0x544D/EthernetLEDCube/PCB/schaltplan.pdf

# Vorwiderstände: Rot: 129 Ohm -> 20 mA

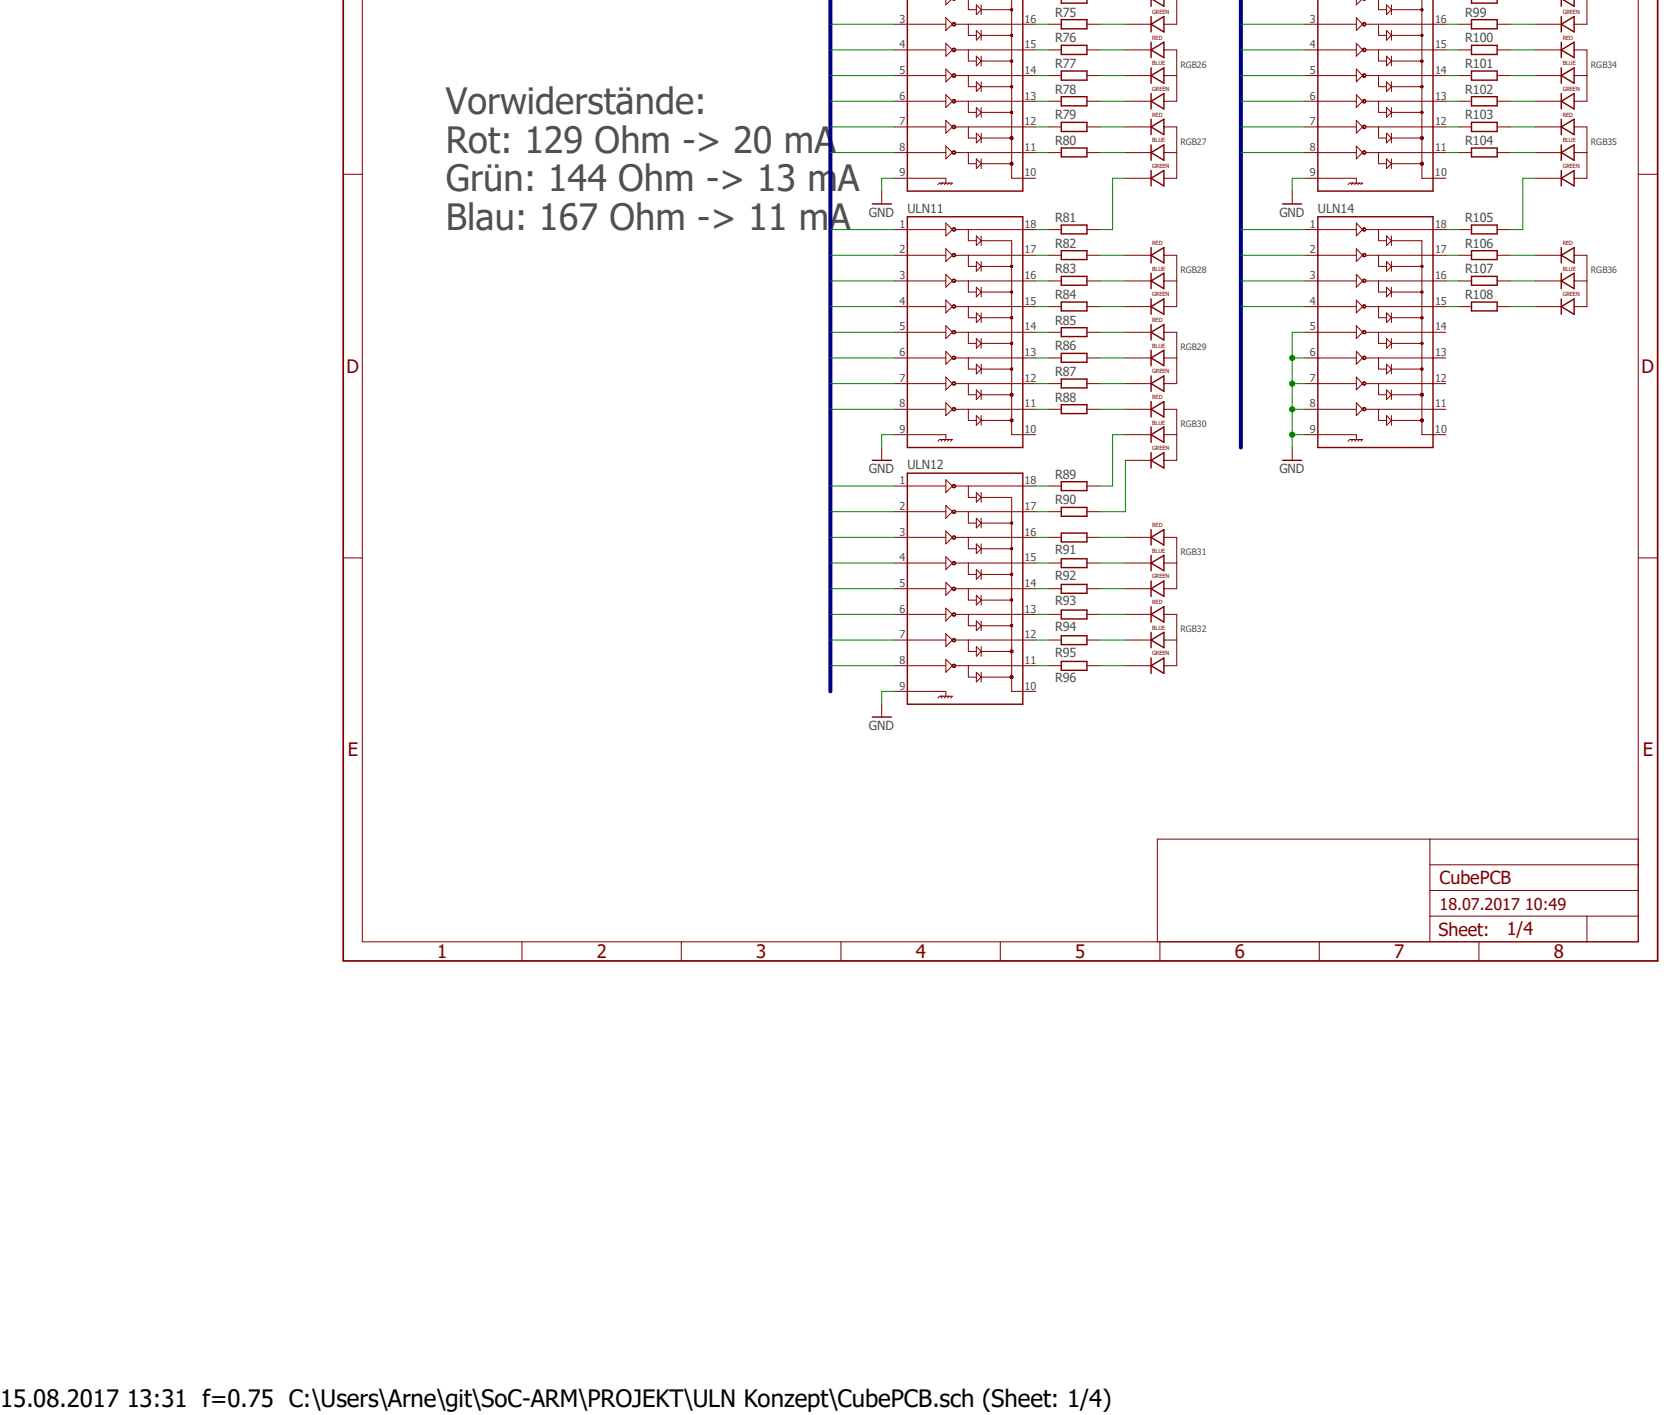
[picture p20: page 1]

Grün: 144 Ohm -> 13 mA
Blau: 167 Ohm -> 11 mA GND

15.08.2017 13:31 f=0.75 C:\Users\Arne\git\SoC-ARM\PROJEKT\ULN Konzept\CubePCB.sch (Sheet: 1/4)

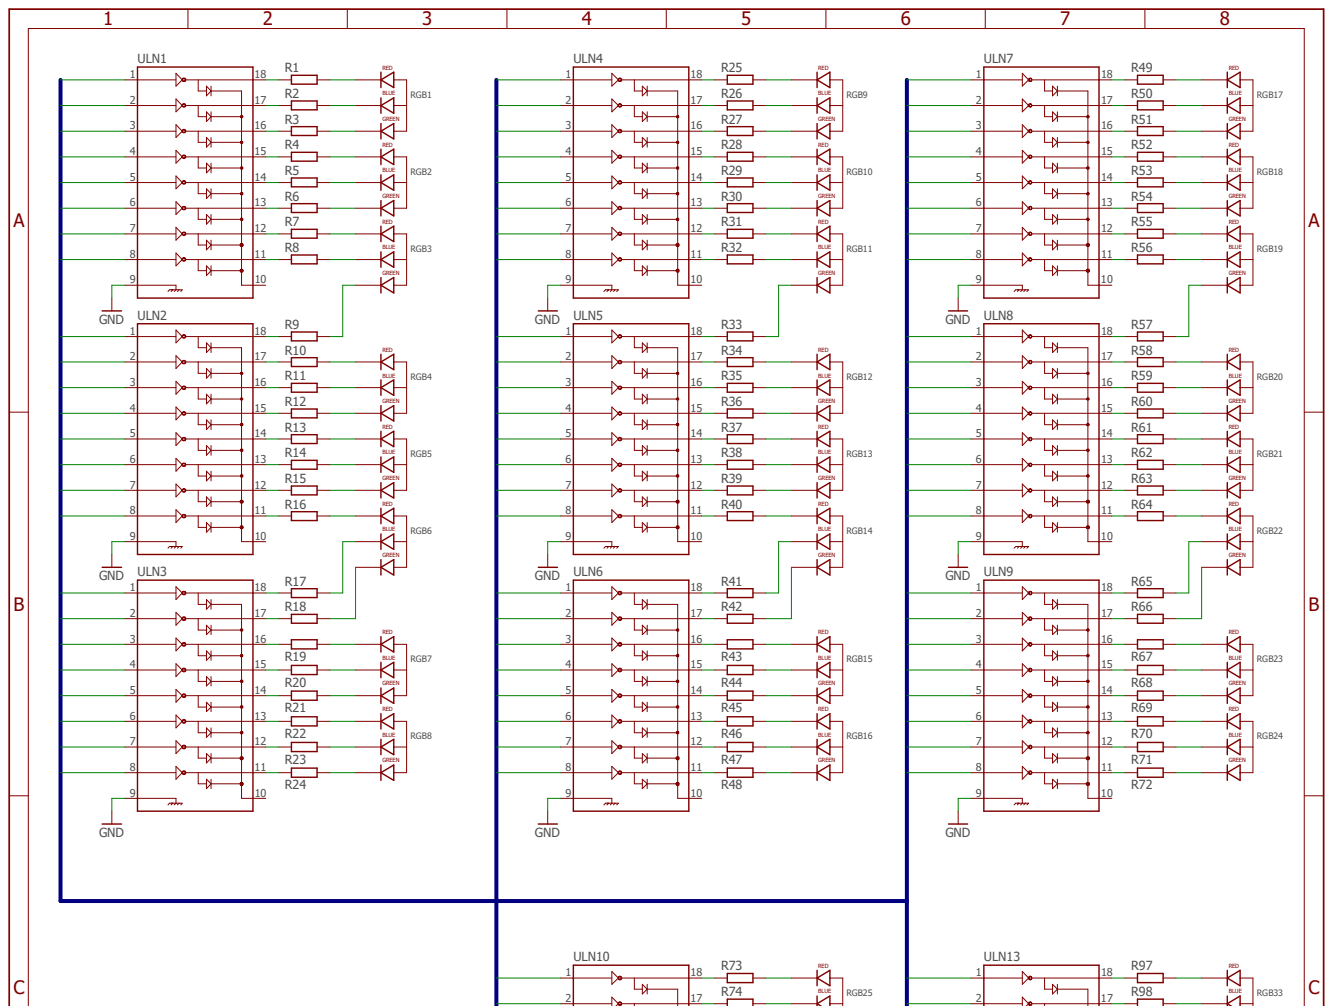
[picture p21: page 2]

# Q11 2 IC1A

A

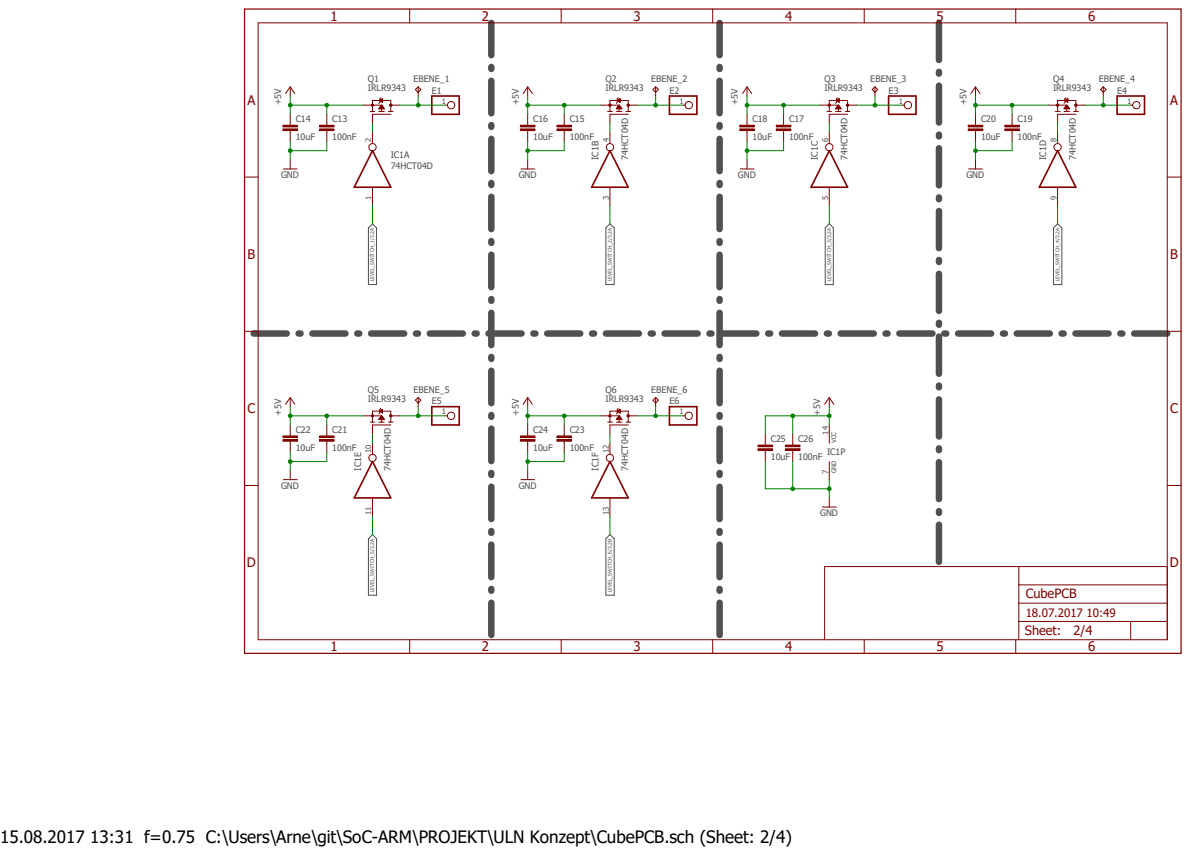
[picture p22: page 3]

EBENE_1 Q2 EBENE_2 Q3 EBENE_3 | Q4 EBENE_4

15.08.2017 13:31 f=0.75 C:\Users\Arne\git\SoC-ARM\PROJEKT\ULN Konzept\CubePCB.sch (Sheet: 2/4)

B36 ⁵V_FPGA_P2 | 3V3_FPGA_P2
B19 ⁵V_FPGA_P1 | 3V3_FPGA_P1 1

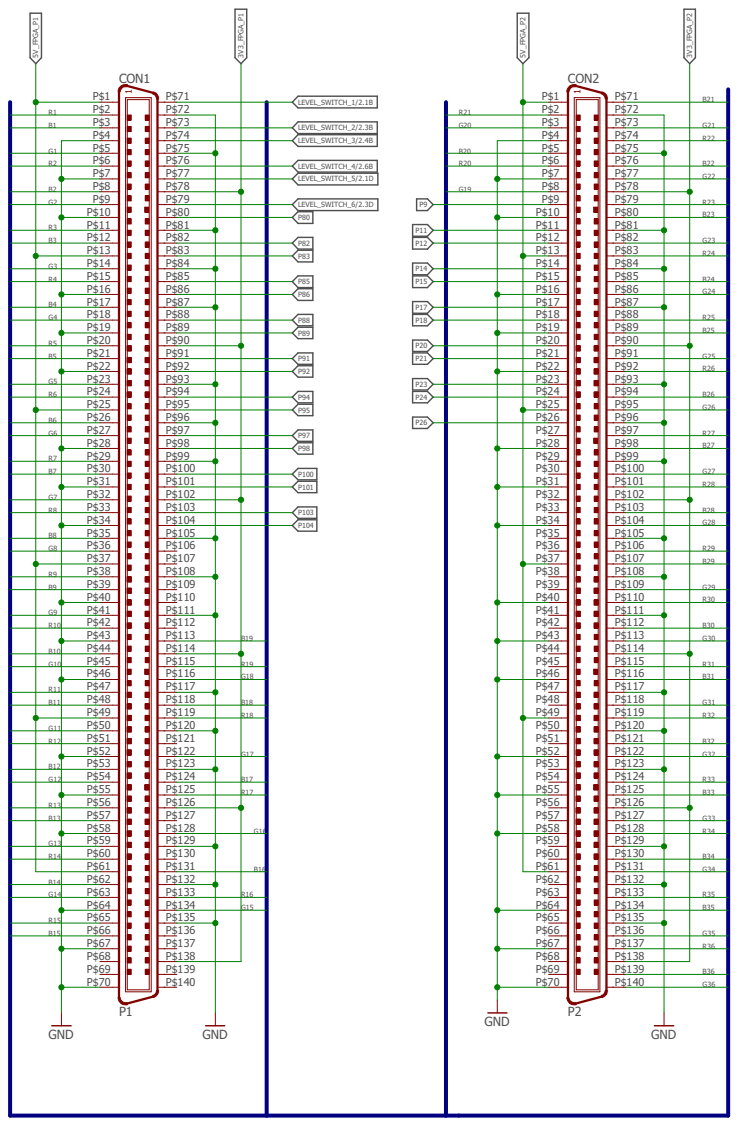
[picture p23: page 4]

15.08.2017 13:31 f=0.75 C:\Users\Arne\git\SoC-ARM\PROJEKT\ULN Konzept\CubePCB.sch (Sheet: 3/4)

A

A

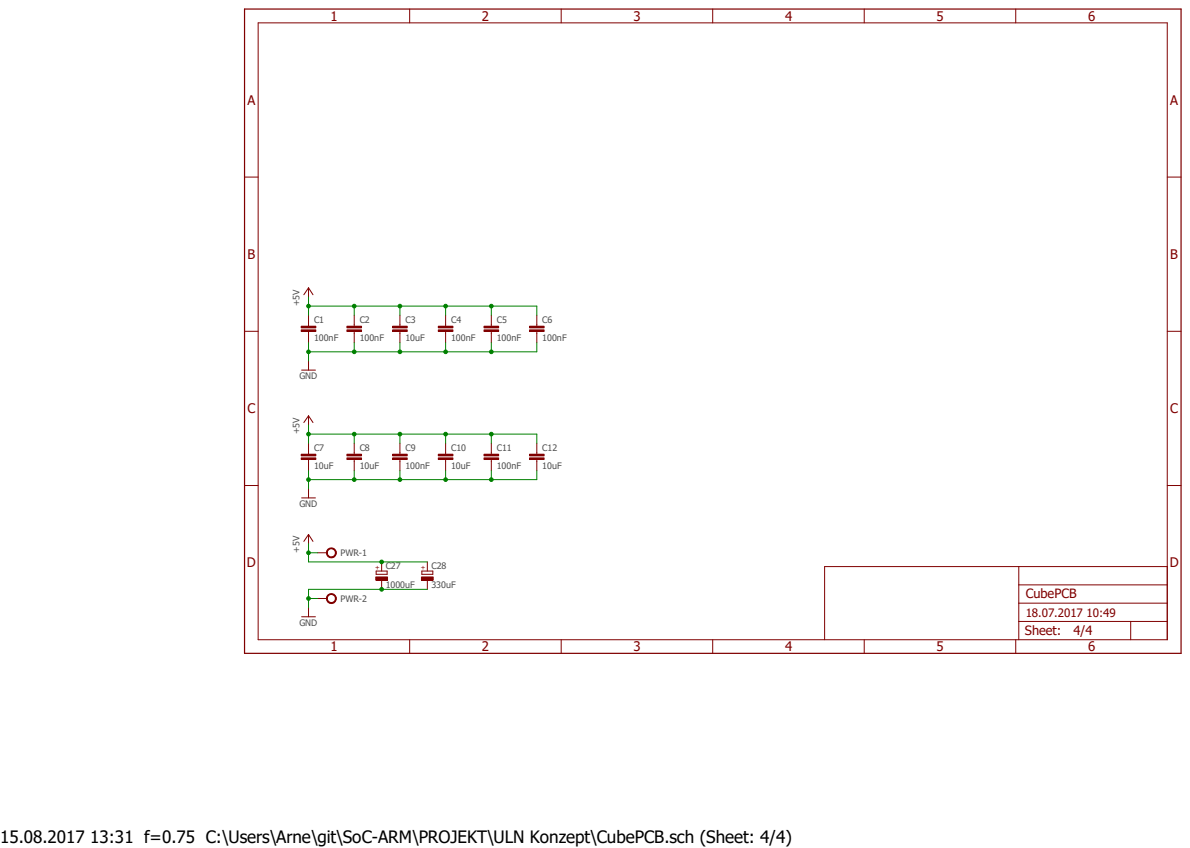
[picture p24: page 5]

15.08.2017 13:31 f=0.75 C:\Users\Arne\git\SoC-ARM\PROJEKT\ULN Konzept\CubePCB.sch (Sheet: 4/4) ⁺⁵V GND
