0x544D/EthernetLEDCube/software/v2/cube.h

#ifndef _CUBE_H
#define _CUBE_H

#include <arpa/inet.h>
#include <linux/if_packet.h>
#include <sys/ioctl.h>
#include <sys/socket.h>
#include <net/if.h>
#include <netinet/ether.h>

#define FPGA_MAC_ADDR0	0xaa
#define FPGA_MAC_ADDR1	0xaa
#define FPGA_MAC_ADDR2	0xaa
#define FPGA_MAC_ADDR3	0xaa
#define FPGA_MAC_ADDR4	0xaa
#define FPGA_MAC_ADDR5	0xaa

#define INTERFACE	"enp0s3"
#define BUF_SIZ		122

#define BUF_PAYLOAD_BEGIN	14
#define CUBE_DIM	6
#define PWM_STEPS	256

typedef struct {
	uint8_t r;
	uint8_t g;
	uint8_t b;
} led;

typedef struct {
	uint16_t h;
	float s;
	float v;
} hsvColor;


pthread_mutex_t ledCubeMutex;

led ledCube0[CUBE_DIM][CUBE_DIM][CUBE_DIM];
led ledCube1[CUBE_DIM][CUBE_DIM][CUBE_DIM];

led (*showLedCube)[CUBE_DIM][CUBE_DIM][CUBE_DIM];
led (*drawLedCube)[CUBE_DIM][CUBE_DIM][CUBE_DIM];


pthread_mutex_t etherFrameMutex;

char etherFrameBuff0[BUF_SIZ];
char etherFrameBuff1[BUF_SIZ];

char* sendBuf;
char* sendMsg;


struct ether_header *eh0;
struct ether_header *eh1;

int sockfd;
struct ifreq if_idx;
struct ifreq if_mac;
int tx_len;

struct sockaddr_ll socket_address;

void initEthernet();
void *ethSend(void *);
void *cubePWMController(void *);
void *cubeAnimator(void *);

void cubeSetAnimationMode(uint8_t nextMode);

void startTimeMeasurement();
void delayExecutionTimeCompensated(uint64_t uSec);

void swapLedCubeBuffers();




#endif
